florian-coder/Inktime-SmartWatch---Susai-Florian-332CA/Images/Screenshot 2026-04-15 184715.png

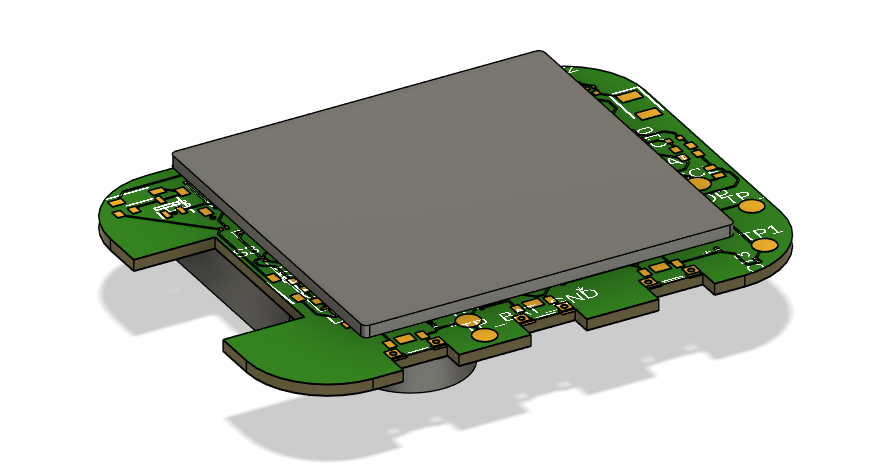
Images/Screenshot 2026-04-15 184715.png
