florian-coder/Inktime-SmartWatch---Susai-Florian-332CA/Images/Screenshot 2026-04-18 005944.png

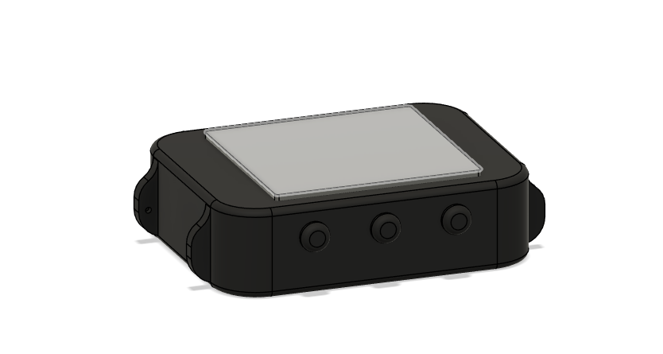
Images/Screenshot 2026-04-18 005944.png
