florian-coder/Inktime-SmartWatch---Susai-Florian-332CA/Images/Screenshot 2026-04-18 010449.png

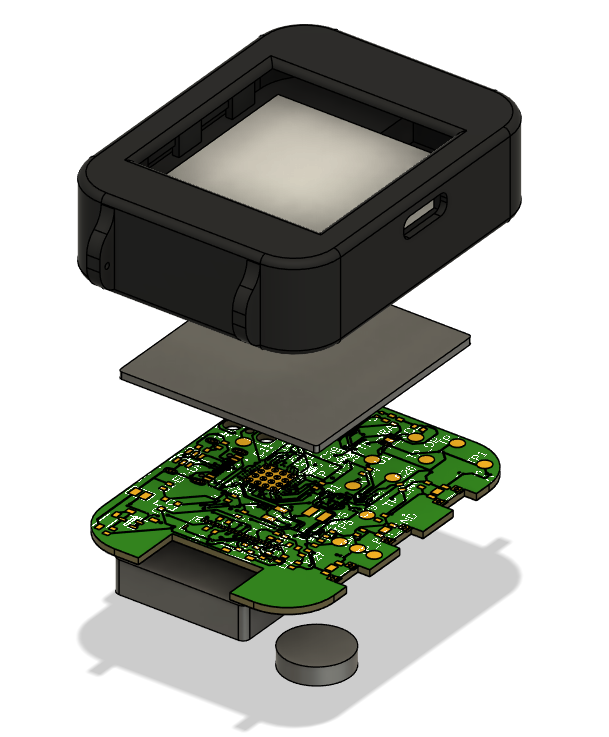
Images/Screenshot 2026-04-18 010449.png
